AbdiYus/XIAO-ESP32C3-bluetooth-macropad/Code/code/pins.h

/**
*   This file contains the pin definitions for the keypad 
*   and the LED.   
*
*   @file pins.h
*   @author Abdirahman Ahmed Yusuf
*/
#ifndef PINS_H
#define PINS_H

/*  Keyboard  */ 
#define col_1 D9
#define col_2 D10
#define row_1 D1
#define row_2 D0

/*  Encoder  */
#define input_a D7
#define input_b D8
#define encoder_pin D6 

/*  Sleep mode  */
#define sleep_timeout 300000

#endif
